NajidPI/GBC_RPi/motherboard_front.jpg

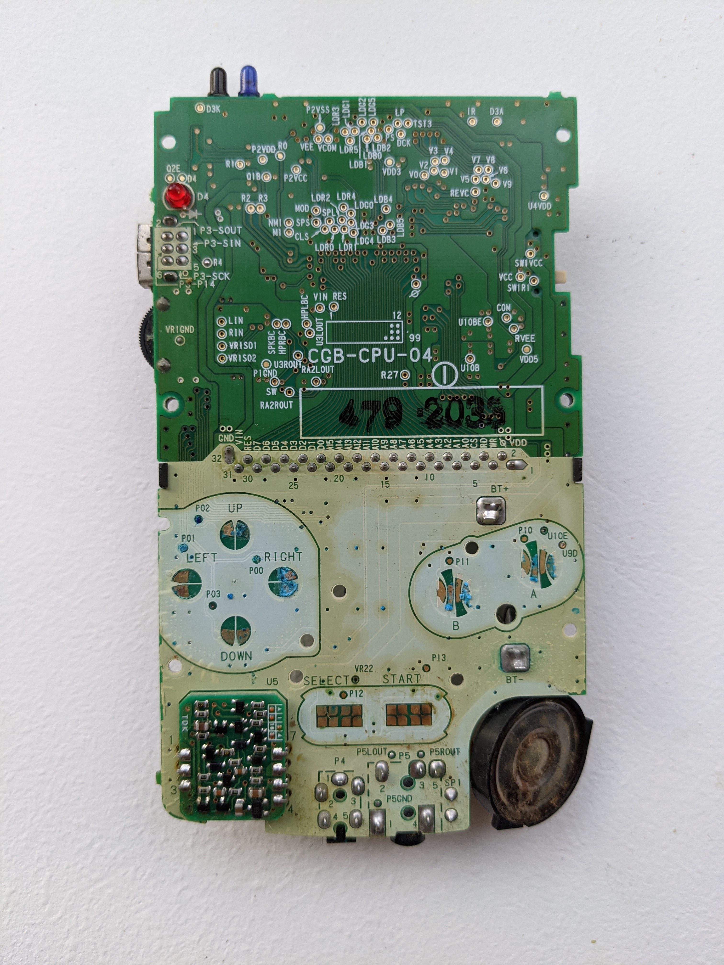
motherboard_front.jpg
