NajidPI/GBC_RPi/GBC_controller_board.jpg

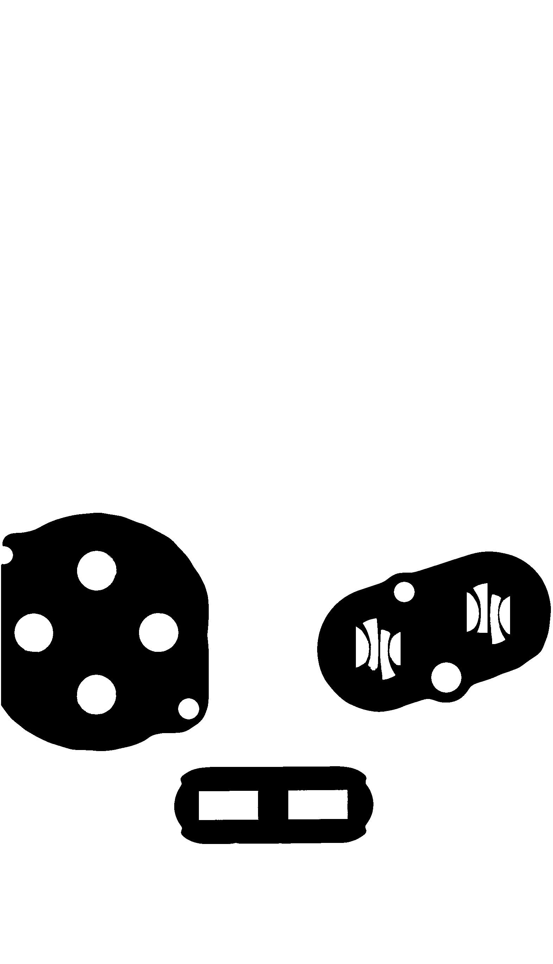
GBC_controller_board.jpg
