NajidPI/GBC_RPi/outline_2.jpg

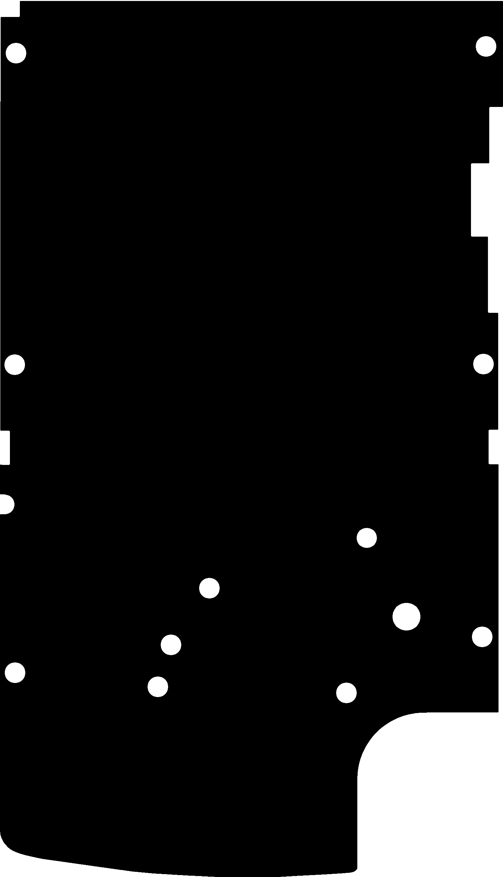
outline_2.jpg
