NajidPI/GBC_RPi/pikachu.jpg

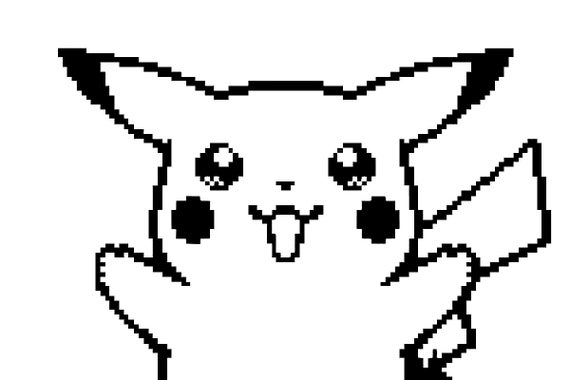
pikachu.jpg
